Misaka0x2730/MioLink/firmware/source/bmp/jtagtap.c

/*
 * This file is part of the Black Magic Debug project.
 *
 * Copyright (C) 2011  Black Sphere Technologies Ltd.
 * Written by Gareth McMullin <gareth@blacksphere.co.nz>
 * Copyright (C) 2022-2023 1BitSquared <info@1bitsquared.com>
 * Modified by Rachel Mant <git@dragonmux.network>
 * Modified by Dmitry Rezvanov <dmitry.rezvanov@yandex.ru>
 *
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
 * You should have received a copy of the GNU General Public License
 * along with this program.  If not, see <http://www.gnu.org/licenses/>.
 */

/* This file implements the low-level JTAG TAP interface.  */

#include "general.h"

#include "platform.h"

#include "tap_pio.h"

#include "jtagtap.h"

#include "pio_jtag.pio.h"

#define TARGET_JTAG_TICKS_NO_FINAL(ticks) (ticks - 1)
#define TARGET_JTAG_TICKS_FINAL(ticks)    (ticks - 2)

typedef enum {
	TARGET_JTAG_SET_INITIAL_0 = 0,
	TARGET_JTAG_SET_INITIAL_1 = 1,
} target_jtag_set_initial_t;

typedef enum {
	TARGET_JTAG_SET_FINAL_NO = 0,
	TARGET_JTAG_SET_FINAL_0 = 1,
	TARGET_JTAG_SET_FINAL_1 = 2,
} target_jtag_set_final_t;

jtag_proc_s jtag_proc;

static void jtagtap_reset(void);
static void jtagtap_tms_seq(uint32_t tms_states, size_t ticks);
static void jtagtap_tdi_tdo_seq(uint8_t *data_out, bool final_tms, const uint8_t *data_in, size_t clock_cycles);
static void jtagtap_tdi_seq(bool final_tms, const uint8_t *data_in, size_t clock_cycles);
static bool jtagtap_next(bool tms, bool tdi);
static void jtagtap_cycle(bool tms, bool tdi, size_t clock_cycles);

void jtagtap_init(void)
{
	tap_pio_disable_all_machines(TAP_PIO_SWD);
	tap_pio_disable_all_machines(TAP_PIO_JTAG);

	const platform_target_pins_t *target_pins = platform_get_target_pins();

	if (target_pins->tms_dir != PIN_NOT_CONNECTED) {
		gpio_init(target_pins->tms_dir);
		gpio_set_dir(target_pins->tms_dir, GPIO_OUT);
		gpio_put(target_pins->tms_dir, true);
	}

	gpio_init(target_pins->tck);
	pio_gpio_init(TAP_PIO_JTAG, target_pins->tck);

	gpio_init(target_pins->tdo);
	gpio_set_pulls(target_pins->tdo, true, false);
	pio_gpio_init(TAP_PIO_JTAG, target_pins->tdo);

	gpio_init(target_pins->tdi);
	pio_gpio_init(TAP_PIO_JTAG, target_pins->tdi);

	gpio_init(target_pins->tms);
	pio_gpio_init(TAP_PIO_JTAG, target_pins->tms);

	pio_clear_instruction_memory(TAP_PIO_JTAG);

	const uint32_t pindirs_value = (1 << target_pins->tck) | (1 << target_pins->tdi) | (1 << target_pins->tms);
	const uint32_t pindirs_mask =
		(1 << target_pins->tck) | (1 << target_pins->tdi) | (1 << target_pins->tdo) | (1 << target_pins->tms);
	const uint32_t pins_value = 0;
	const uint32_t pins_mask = (1 << target_pins->tck) | (1 << target_pins->tdi) | (1 << target_pins->tms);

	pio_sm_set_pindirs_with_mask(TAP_PIO_JTAG, TAP_PIO_SM_JTAG_TDI_TDO_SEQ, pindirs_value, pindirs_mask);
	pio_sm_set_pins_with_mask(TAP_PIO_JTAG, TAP_PIO_SM_JTAG_TDI_TDO_SEQ, pins_value, pins_mask);

	tap_pio_disable_input_sync(TAP_PIO_JTAG, target_pins->tdo);

	pio_add_program_at_offset(TAP_PIO_JTAG, &target_jtag_program, target_jtag_program.origin);

	pio_sm_config prog_config = target_jtag_program_get_default_config(0);

	/* JTAG TDI/TDO sequence SM */
	sm_config_set_in_pins(&prog_config, target_pins->tdo);
	sm_config_set_out_pins(&prog_config, target_pins->tdi, 1);
	sm_config_set_sideset_pins(&prog_config, target_pins->tck);
	sm_config_set_set_pins(&prog_config, target_pins->tms, 1);
	sm_config_set_out_shift(&prog_config, true, true, 8);
	sm_config_set_in_shift(&prog_config, true, true, 8);

	pio_sm_init(TAP_PIO_JTAG, TAP_PIO_SM_JTAG_TDI_TDO_SEQ, target_jtag_program.origin, &prog_config);
	pio_sm_set_enabled(TAP_PIO_JTAG, TAP_PIO_SM_JTAG_TDI_TDO_SEQ, false);

	/* JTAG TMS sequence SM */
	sm_config_set_in_pins(&prog_config, target_pins->tdo);
	sm_config_set_out_pins(&prog_config, target_pins->tms, 1);
	sm_config_set_sideset_pins(&prog_config, target_pins->tck);
	sm_config_set_set_pins(&prog_config, target_pins->tdi, 1);
	sm_config_set_out_shift(&prog_config, true, true, 8);
	sm_config_set_in_shift(&prog_config, true, true, 8);

	pio_sm_init(TAP_PIO_JTAG, TAP_PIO_SM_JTAG_TMS_SEQ, target_jtag_program.origin, &prog_config);
	pio_sm_set_enabled(TAP_PIO_JTAG, TAP_PIO_SM_JTAG_TMS_SEQ, false);

	platform_max_frequency_set(platform_max_frequency_get());

	jtag_proc.jtagtap_reset = jtagtap_reset;
	jtag_proc.jtagtap_next = jtagtap_next;
	jtag_proc.jtagtap_tms_seq = jtagtap_tms_seq;
	jtag_proc.jtagtap_tdi_tdo_seq = jtagtap_tdi_tdo_seq;
	jtag_proc.jtagtap_tdi_seq = jtagtap_tdi_seq;
	jtag_proc.jtagtap_cycle = jtagtap_cycle;
	jtag_proc.tap_idle_cycles = 1;

	/* Ensure we're in JTAG mode */
	for (size_t i = 0; i <= 50U; ++i)
		jtagtap_next(true, false); /* 50 + 1 idle cycles for SWD reset */
	jtagtap_tms_seq(0xe73cU, 16U); /* SWD to JTAG sequence */
}

static void jtagtap_reset(void)
{
	jtagtap_soft_reset();
}

static bool jtagtap_next(const bool tms, const bool tdi)
{
	uint8_t pio_buffer[TAP_PIO_DMA_BUF_SIZE] = {0};
	uint8_t data_amount = 0;

	pio_sm_set_enabled(TAP_PIO_JTAG, TAP_PIO_SM_JTAG_TDI_TDO_SEQ, true);

	pio_buffer[data_amount++] = TARGET_JTAG_TICKS_NO_FINAL(1);
	pio_buffer[data_amount++] = (tms ? TARGET_JTAG_SET_INITIAL_1 : TARGET_JTAG_SET_INITIAL_0);
	pio_buffer[data_amount++] = TARGET_JTAG_SET_FINAL_NO;
	pio_buffer[data_amount++] = (tdi ? 1 : 0);

	tap_pio_dma_send_uint8(TAP_PIO_JTAG, TAP_PIO_SM_JTAG_TDI_TDO_SEQ, pio_buffer, data_amount);
	const bool result = (pio_sm_get_blocking(TAP_PIO_JTAG, TAP_PIO_SM_JTAG_TDI_TDO_SEQ) != 0);

	pio_sm_clear_fifos(TAP_PIO_JTAG, TAP_PIO_SM_JTAG_TDI_TDO_SEQ);
	pio_sm_set_enabled(TAP_PIO_JTAG, TAP_PIO_SM_JTAG_TDI_TDO_SEQ, false);

	return result;
}

static void jtagtap_tms_seq(const uint32_t tms_states, const size_t ticks)
{
	uint8_t pio_buffer[TAP_PIO_DMA_BUF_SIZE] = {0};
	uint8_t data_amount = 0;

	pio_sm_set_enabled(TAP_PIO_JTAG, TAP_PIO_SM_JTAG_TMS_SEQ, true);

	pio_buffer[data_amount++] = TARGET_JTAG_TICKS_NO_FINAL(ticks);
	pio_buffer[data_amount++] = TARGET_JTAG_SET_INITIAL_1;
	pio_buffer[data_amount++] = TARGET_JTAG_SET_FINAL_NO;

	size_t data_bytes = ticks / 8;
	if (ticks % 8) {
		data_bytes++;
	}

	for (uint8_t i = 0; (i < data_bytes); i++) {
		pio_buffer[data_amount++] = ((tms_states >> (8 * i)) & 0xFF);
	}

	tap_pio_dma_send_recv_uint8(TAP_PIO_JTAG, TAP_PIO_SM_JTAG_TMS_SEQ, pio_buffer, NULL, data_amount, data_bytes);
	tap_pio_wait_for_tx_stall(TAP_PIO_JTAG, TAP_PIO_SM_JTAG_TMS_SEQ);

	pio_sm_clear_fifos(TAP_PIO_JTAG, TAP_PIO_SM_JTAG_TMS_SEQ);
	pio_sm_set_enabled(TAP_PIO_JTAG, TAP_PIO_SM_JTAG_TMS_SEQ, false);
}

static void jtagtap_tdi_tdo_seq(
	uint8_t *const data_out, const bool final_tms, const uint8_t *const data_in, size_t clock_cycles)
{
	uint8_t pio_buffer[TAP_PIO_DMA_BUF_SIZE] = {0};
	uint8_t data_amount = 0;

	if (clock_cycles == 0) {
		return;
	}

	pio_sm_set_enabled(TAP_PIO_JTAG, TAP_PIO_SM_JTAG_TDI_TDO_SEQ, true);

	if (clock_cycles == 1) {
		pio_buffer[data_amount++] = TARGET_JTAG_TICKS_NO_FINAL(1);
		pio_buffer[data_amount++] = (final_tms ? TARGET_JTAG_SET_INITIAL_1 : TARGET_JTAG_SET_INITIAL_0);
		pio_buffer[data_amount++] = TARGET_JTAG_SET_FINAL_NO;
		pio_buffer[data_amount++] = data_in[0];

		tap_pio_dma_send_recv_uint8(TAP_PIO_JTAG, TAP_PIO_SM_JTAG_TDI_TDO_SEQ, pio_buffer, data_out, data_amount, 1);
		data_out[0] >>= 7;
	} else {
		pio_buffer[data_amount++] = TARGET_JTAG_TICKS_FINAL(clock_cycles);
		pio_buffer[data_amount++] = TARGET_JTAG_SET_INITIAL_0;
		pio_buffer[data_amount++] = (final_tms ? TARGET_JTAG_SET_FINAL_1 : TARGET_JTAG_SET_FINAL_0);

		size_t data_bytes = clock_cycles / 8;
		if (clock_cycles % 8) {
			data_bytes++;
		}

		assert((data_amount + data_bytes) <= TAP_PIO_DMA_BUF_SIZE);
		memcpy(&(pio_buffer[data_amount]), data_in, data_bytes);

		data_amount += data_bytes;

		size_t data_out_cnt = tap_pio_dma_send_recv_uint8(
			TAP_PIO_JTAG, TAP_PIO_SM_JTAG_TDI_TDO_SEQ, pio_buffer, data_out, data_amount, data_bytes);

		if ((clock_cycles % 8) != 0) {
			data_out[data_out_cnt - 1] >>= (8 - (clock_cycles % 8));
		}
	}

	tap_pio_wait_for_tx_stall(TAP_PIO_JTAG, TAP_PIO_SM_JTAG_TDI_TDO_SEQ);

	pio_sm_clear_fifos(TAP_PIO_JTAG, TAP_PIO_SM_JTAG_TDI_TDO_SEQ);
	pio_sm_set_enabled(TAP_PIO_JTAG, TAP_PIO_SM_JTAG_TDI_TDO_SEQ, false);
}

static void jtagtap_tdi_seq(const bool final_tms, const uint8_t *const data_in, const size_t clock_cycles)
{
	uint8_t pio_buffer[TAP_PIO_DMA_BUF_SIZE] = {0};
	uint8_t data_amount = 0;

	if (clock_cycles == 0) {
		return;
	}

	pio_sm_set_enabled(TAP_PIO_JTAG, TAP_PIO_SM_JTAG_TDI_TDO_SEQ, true);

	if (clock_cycles == 1) {
		pio_buffer[data_amount++] = TARGET_JTAG_TICKS_NO_FINAL(1);
		pio_buffer[data_amount++] = (final_tms ? TARGET_JTAG_SET_INITIAL_1 : TARGET_JTAG_SET_INITIAL_0);
		pio_buffer[data_amount++] = TARGET_JTAG_SET_FINAL_NO;
		pio_buffer[data_amount++] = data_in[0];

		tap_pio_dma_send_recv_uint8(TAP_PIO_JTAG, TAP_PIO_SM_JTAG_TDI_TDO_SEQ, pio_buffer, NULL, data_amount, 1);
	} else {
		pio_buffer[data_amount++] = TARGET_JTAG_TICKS_FINAL(clock_cycles);
		pio_buffer[data_amount++] = TARGET_JTAG_SET_INITIAL_0;
		pio_buffer[data_amount++] = (final_tms ? TARGET_JTAG_SET_FINAL_1 : TARGET_JTAG_SET_FINAL_0);

		size_t data_bytes = clock_cycles / 8;
		if (clock_cycles % 8) {
			data_bytes++;
		}

		assert((data_amount + data_bytes) <= TAP_PIO_DMA_BUF_SIZE);
		memcpy(&(pio_buffer[data_amount]), data_in, data_bytes);

		data_amount += data_bytes;

		tap_pio_dma_send_recv_uint8(
			TAP_PIO_JTAG, TAP_PIO_SM_JTAG_TDI_TDO_SEQ, pio_buffer, NULL, data_amount, data_bytes);
	}

	tap_pio_wait_for_tx_stall(TAP_PIO_JTAG, TAP_PIO_SM_JTAG_TDI_TDO_SEQ);

	pio_sm_clear_fifos(TAP_PIO_JTAG, TAP_PIO_SM_JTAG_TDI_TDO_SEQ);
	pio_sm_set_enabled(TAP_PIO_JTAG, TAP_PIO_SM_JTAG_TDI_TDO_SEQ, false);
}

static void jtagtap_cycle(const bool tms, const bool tdi, const size_t clock_cycles)
{
	uint8_t pio_buffer[TAP_PIO_DMA_BUF_SIZE] = {0};
	uint8_t data_amount = 0;

	pio_sm_set_enabled(TAP_PIO_JTAG, TAP_PIO_SM_JTAG_TDI_TDO_SEQ, true);

	pio_buffer[data_amount++] = TARGET_JTAG_TICKS_NO_FINAL(clock_cycles);
	pio_buffer[data_amount++] = (tms ? TARGET_JTAG_SET_INITIAL_1 : TARGET_JTAG_SET_INITIAL_0);
	pio_buffer[data_amount++] = TARGET_JTAG_SET_FINAL_NO;

	size_t data_bytes = clock_cycles / 8;
	if (clock_cycles % 8) {
		data_bytes++;
	}

	memset(&(pio_buffer[data_amount]), (tdi ? 0xFF : 0), data_bytes);

	data_amount += data_bytes;

	tap_pio_dma_send_recv_uint8(TAP_PIO_JTAG, TAP_PIO_SM_JTAG_TDI_TDO_SEQ, pio_buffer, NULL, data_amount, data_bytes);

	tap_pio_wait_for_tx_stall(TAP_PIO_JTAG, TAP_PIO_SM_JTAG_TDI_TDO_SEQ);

	pio_sm_clear_fifos(TAP_PIO_JTAG, TAP_PIO_SM_JTAG_TDI_TDO_SEQ);
	pio_sm_set_enabled(TAP_PIO_JTAG, TAP_PIO_SM_JTAG_TDI_TDO_SEQ, false);
}
