Misaka0x2730/MioLink/firmware/include/bmp/rp_uart.h

/*
 * This file is part of the MioLink project.
 *
 * Copyright (C) 2024 Dmitry Rezvanov <dmitry.rezvanov@yandex.ru>
 *
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
 * You should have received a copy of the GNU General Public License
 * along with this program.  If not, see <http://www.gnu.org/licenses/>.
 */

#ifndef MIOLINK_RP_UART_H
#define MIOLINK_RP_UART_H

#include "general.h"

#include "hardware/clocks.h"
#include "hardware/uart.h"

#define RP_UART_INT_RX_BITS         (UART_UARTMIS_RXMIS_BITS)
#define RP_UART_INT_RX_TIMEOUT_BITS (UART_UARTMIS_RTMIS_BITS)
#define RP_UART_INT_OE_BITS         (UART_UARTMIS_OEMIS_BITS)

static inline void rp_uart_set_dma_req_enabled(uart_inst_t *uart, const bool rx, const bool tx)
{
	uart_get_hw(uart)->dmacr =
		(bool_to_bit(rx) << UART_UARTDMACR_RXDMAE_LSB) | (bool_to_bit(tx) << UART_UARTDMACR_TXDMAE_LSB);
}

static inline void rp_uart_set_rx_and_timeout_irq_enabled(uart_inst_t *uart, const bool rx, const bool rx_timeout)
{
	hw_write_masked(&uart_get_hw(uart)->imsc,
		(bool_to_bit(rx) << UART_UARTIMSC_RXIM_LSB) | (bool_to_bit(rx_timeout) << UART_UARTIMSC_RTIM_LSB),
		UART_UARTIMSC_RXIM_BITS | UART_UARTIMSC_RTIM_BITS);
}

static inline void rp_uart_set_rx_irq_enabled(uart_inst_t *uart, const bool enabled)
{
	hw_write_masked(
		&uart_get_hw(uart)->imsc, (bool_to_bit(enabled) << UART_UARTIMSC_RXIM_LSB), UART_UARTIMSC_RXIM_BITS);
}

static inline void rp_uart_clear_rx_irq_flag(uart_inst_t *uart)
{
	hw_set_bits(&uart_get_hw(uart)->icr, UART_UARTICR_RXIC_BITS);
}

static inline void rp_uart_clear_rx_timeout_irq_flag(uart_inst_t *uart)
{
	hw_set_bits(&uart_get_hw(uart)->icr, UART_UARTICR_RTIC_BITS);
}

static inline void rp_uart_clear_rx_and_rx_timeout_irq_flags(uart_inst_t *uart)
{
	hw_set_bits(&uart_get_hw(uart)->icr, UART_UARTICR_RXIC_BITS | UART_UARTICR_RTIC_BITS);
}

static inline void rp_uart_set_rx_timeout_irq_enabled(uart_inst_t *uart, const bool enabled)
{
	hw_write_masked(
		&uart_get_hw(uart)->imsc, (bool_to_bit(enabled) << UART_UARTIMSC_RTIM_LSB), UART_UARTIMSC_RTIM_BITS);
}

static inline void rp_uart_set_int_fifo_levels(uart_inst_t *uart, const uint8_t rx_level, const uint8_t tx_level)
{
	hw_write_masked(&uart_get_hw(uart)->ifls,
		(((uint32_t)rx_level) << UART_UARTIFLS_RXIFLSEL_LSB) | (((uint32_t)tx_level) << UART_UARTIFLS_TXIFLSEL_LSB),
		UART_UARTIFLS_RXIFLSEL_BITS | UART_UARTIFLS_TXIFLSEL_BITS);
}

static inline uint32_t rp_uart_get_int_status(uart_inst_t *uart)
{
	return uart_get_hw(uart)->mis;
}

static inline bool rp_uart_is_rx_fifo_empty(uart_inst_t *uart)
{
	return ((uart_get_hw(uart)->fr & UART_UARTFR_RXFE_BITS) != 0);
}

static inline uint8_t rp_uart_read(uart_inst_t *uart)
{
	return (uint8_t)(uart_get_hw(uart)->dr);
}

static inline void *rp_uart_get_dr_address(uart_inst_t *uart)
{
	return (void *)(&(uart_get_hw(uart)->dr));
}

static inline uint32_t rp_uart_get_baudrate(uart_inst_t *uart)
{
	const uint32_t ibrd = uart_get_hw(uart)->ibrd;
	const uint32_t fbrd = uart_get_hw(uart)->fbrd;
	return (4 * clock_get_hz(UART_CLOCK_NUM(uart))) / (64 * ibrd + fbrd);
}

static inline bool rp_uart_is_transmitting(uart_inst_t *uart)
{
	return ((uart_get_hw(uart)->fr & UART_UARTFR_BUSY_BITS) != 0);
}

#endif /* MIOLINK_RP_UART_H */
