Misaka0x2730/MioLink/firmware/source/bmp/traceswodecode.c

/*
 * This file is part of the Black Magic Debug project.
 *
 * Modified by Dmitry Rezvanov <dmitry.rezvanov@yandex.ru>
 *
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
 * You should have received a copy of the GNU General Public License
 * along with this program.	 If not, see <http://www.gnu.org/licenses/>.
 */

/* Print decoded swo stream on the usb serial */

#include "general.h"

#include "swo.h"
#include "usb_serial.h"

/* SWO decoding */
/* data is static in case swo packet is astride two buffers */
static uint8_t swo_buf[TRACESWO_BUF_SIZE] = {0};
static int swo_buf_len = 0;
static uint32_t swo_decode = 1; /* bitmask of channels to print */
static int swo_pkt_len = 0;     /* decoder state */
static bool swo_print = false;

/* print decoded swo packet on usb serial */
bool traceswo_decode(const void *buf, uint16_t len, const bool flush, const bool drop_if_no_space)
{
	const uint8_t *const data = (const uint8_t *)buf;

	if (usb_serial_get_available() < sizeof(swo_buf)) {
		return drop_if_no_space;
	}

	for (uint16_t i = 0; i < len; i++) {
		const uint8_t ch = data[i];
		if (swo_pkt_len == 0) {                          /* header */
			const uint32_t channel = (uint32_t)ch >> 3U; /* channel number */
			const uint32_t size = ch & 0x7U;             /* drop channel number */
			if (size == 0x01U)
				swo_pkt_len = 1; /* SWO packet 0x01XX */
			else if (size == 0x02U)
				swo_pkt_len = 2; /* SWO packet 0x02XXXX */
			else if (size == 0x03U)
				swo_pkt_len = 4; /* SWO packet 0x03XXXXXXXX */
			swo_print = (swo_pkt_len != 0) && ((swo_decode & (1UL << channel)) != 0UL);
		} else if (swo_pkt_len <= 4) { /* data */
			if (swo_print) {
				swo_buf[swo_buf_len++] = ch;

				if (swo_buf_len == sizeof(swo_buf)) {
					usb_serial_send_to_usb(swo_buf, swo_buf_len, false, true);
					swo_buf_len = 0;
				}
			}

			--swo_pkt_len;
		} else { /* recover */
			swo_buf_len = 0;
			swo_pkt_len = 0;
		}
	}

	if (flush) {
		if (usb_get_config() && gdb_serial_get_dtr()) {
			usb_serial_send_to_usb(swo_buf, swo_buf_len, flush, true);
		}
		swo_buf_len = 0;
	}

	return true;
}

/* set bitmask of swo channels to be decoded */
void traceswo_setmask(uint32_t mask)
{
	swo_decode = mask;
}

/* not truncated */
